mquerostudio/MQ-One/3-KiCad_library/3-3D/STPS140A.stp

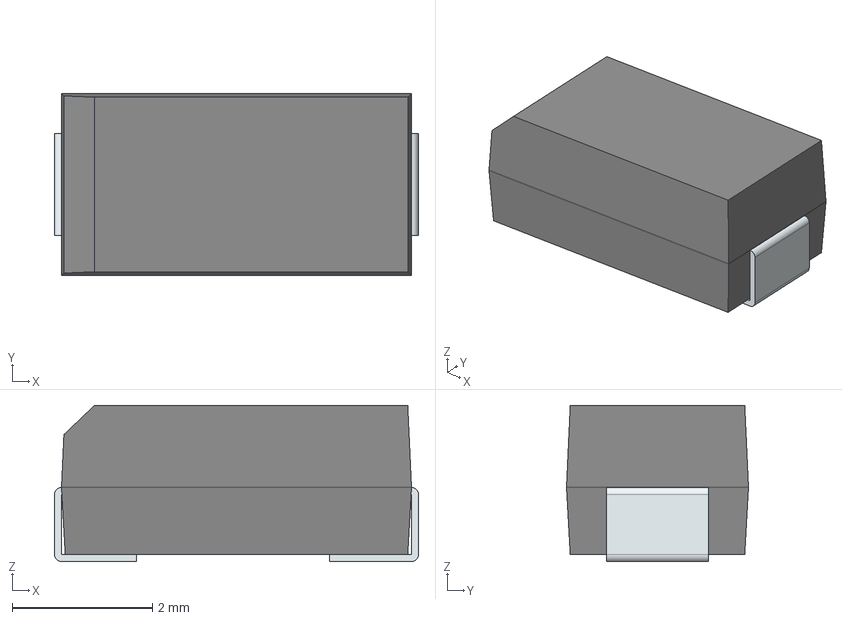
[picture p15: CAD file, 2024-10-10]
3-KiCad_library/3-3D/STPS140A.stp
5.20 x 2.60 x 2.23 mm
FilletPin1
FilletPin2
