mquerostudio/MQ-One/3-KiCad_library/3-3D/SIA527DJ-T1-GE3.stp

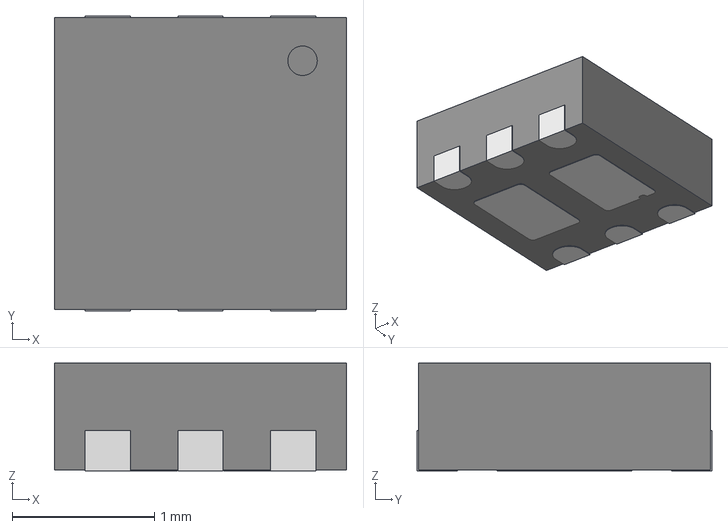
[picture p16: CAD file, 2024-10-10]
3-KiCad_library/3-3D/SIA527DJ-T1-GE3.stp
2.05 x 2.07 x 0.757 mm
