mquerostudio/MQ-One/3-KiCad_library/3-3D/USBLC6-2SC6.stp

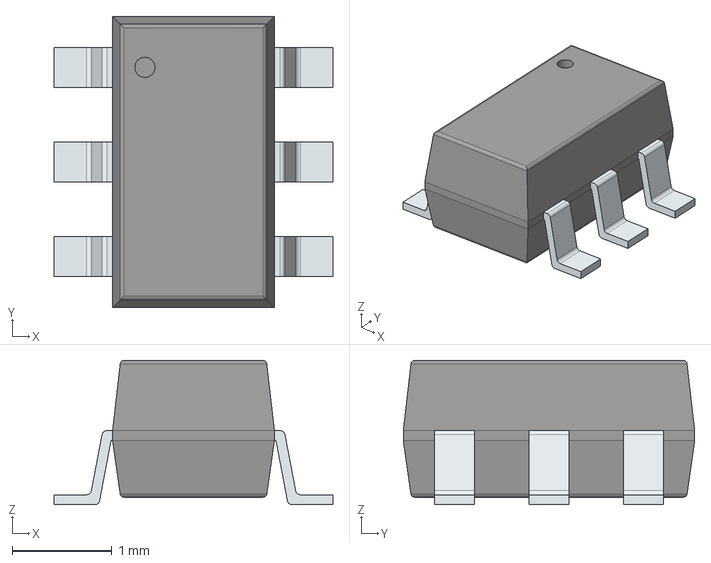
[picture p17: CAD file, 2024-10-10]
3-KiCad_library/3-3D/USBLC6-2SC6.stp
2.80 x 2.92 x 1.45 mm
PinsArrayLR
