mquerostudio/MQ-One/3-KiCad_library/3-3D/2-2328724-1.stp

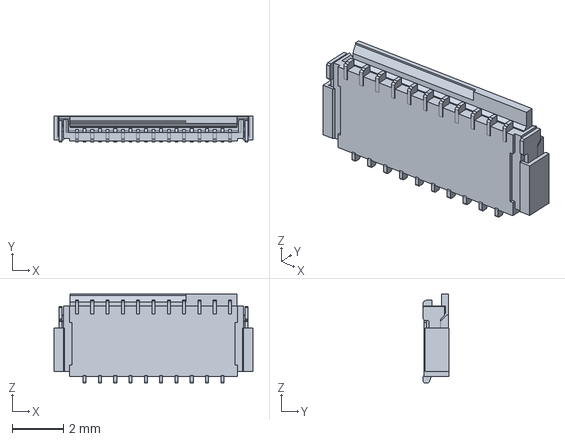
[picture p18: CAD file, 2024-10-10]
3-KiCad_library/3-3D/2-2328724-1.stp
7.80 x 1.00 x 3.48 mm
