mquerostudio/MQ-One/3-KiCad_library/3-3D/S2B-ZR-SM4A-TF.step

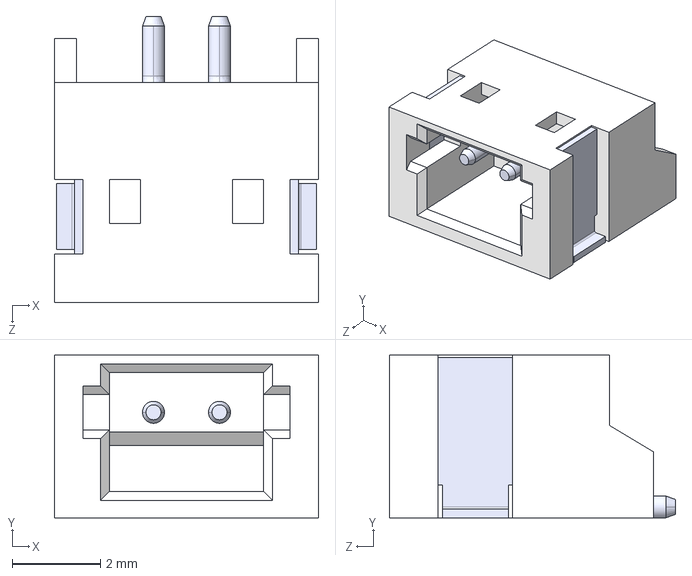
[picture p19: CAD file, 2024-10-10]
3-KiCad_library/3-3D/S2B-ZR-SM4A-TF.step
6.00 x 3.70 x 6.50 mm
