mquerostudio/MQ-One/3-KiCad_library/3-3D/ICS-43434.stp

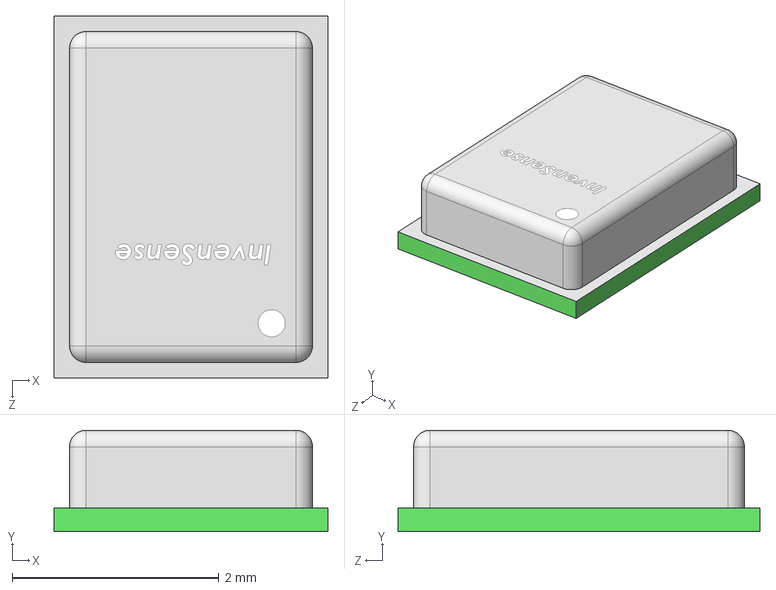
[picture p20: CAD file, 2024-10-10]
3-KiCad_library/3-3D/ICS-43434.stp
2.65 x 0.981 x 3.50 mm
