mquerostudio/MQ-One/3-KiCad_library/3-3D/MSD-1-A.stp

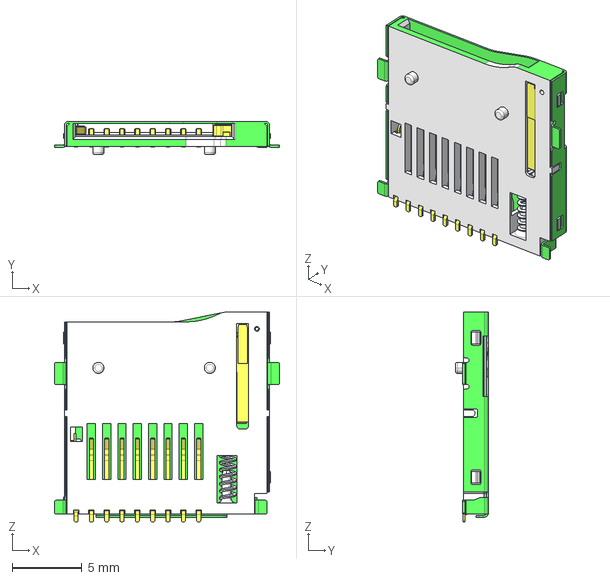
[picture p21: CAD file, 2024-10-10]
3-KiCad_library/3-3D/MSD-1-A.stp
16.1 x 2.40 x 15.0 mm
