mquerostudio/MQ-One/3-KiCad_library/3-3D/ASE-24.000MHZ-L-R-T.stp

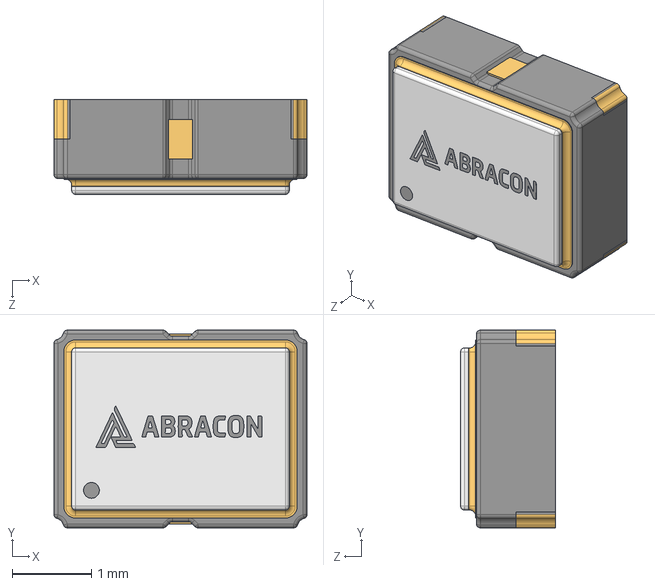
[picture p22: CAD file, 2024-10-10]
3-KiCad_library/3-3D/ASE-24.000MHZ-L-R-T.stp
3.20 x 2.50 x 1.20 mm
ASE-25.000MHZ-LR-T
Abracon New Logo
