mquerostudio/MQ-One/3-KiCad_library/3-3D/DSK-3R3H224U-HL.step

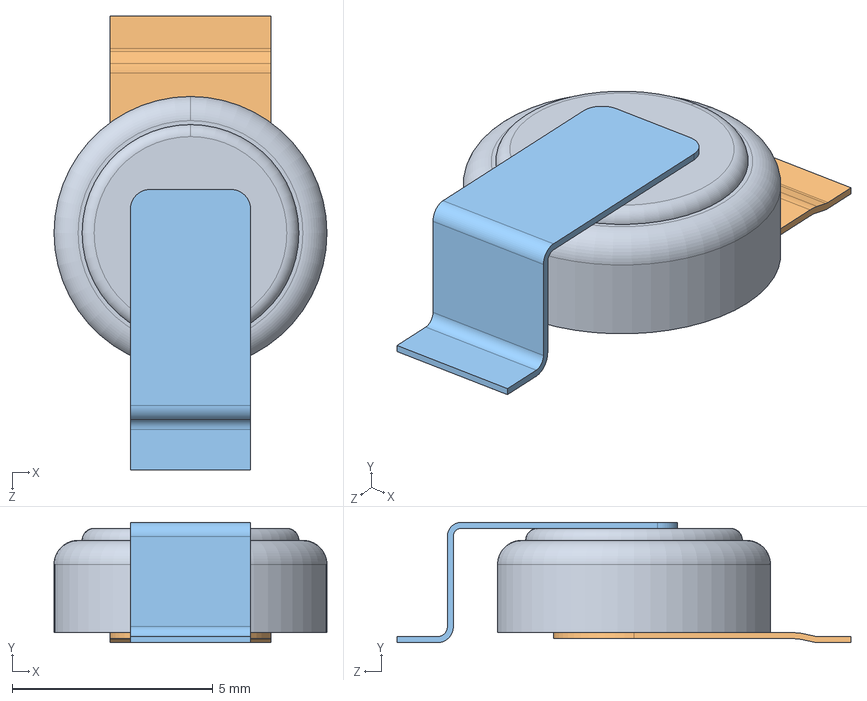
[picture p23: CAD file, 2024-10-10]
3-KiCad_library/3-3D/DSK-3R3H224U-HL.step
6.80 x 3.00 x 11.3 mm
