mquerostudio/MQ-One/3-KiCad_library/3-3D/FH35C-21S-0.3SHW.stp

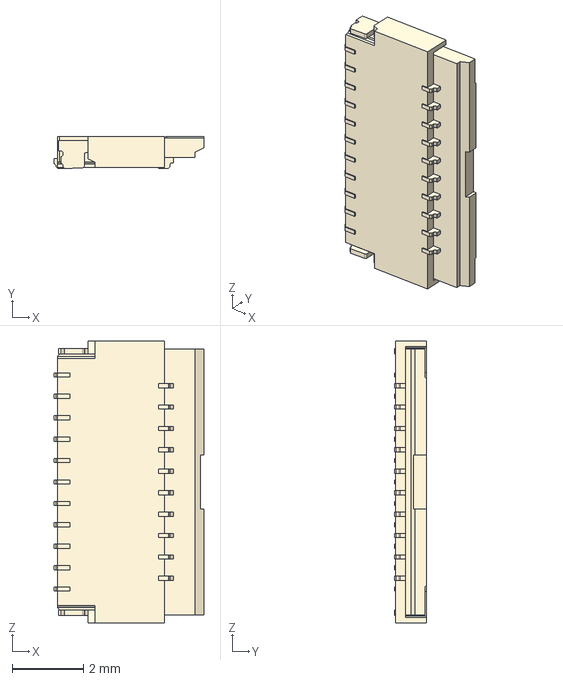
[picture p24: CAD file, 2024-10-10]
3-KiCad_library/3-3D/FH35C-21S-0.3SHW.stp
4.20 x 0.9 x 7.90 mm
