mquerostudio/MQ-One/3-KiCad_library/3-3D/PA1010D.step

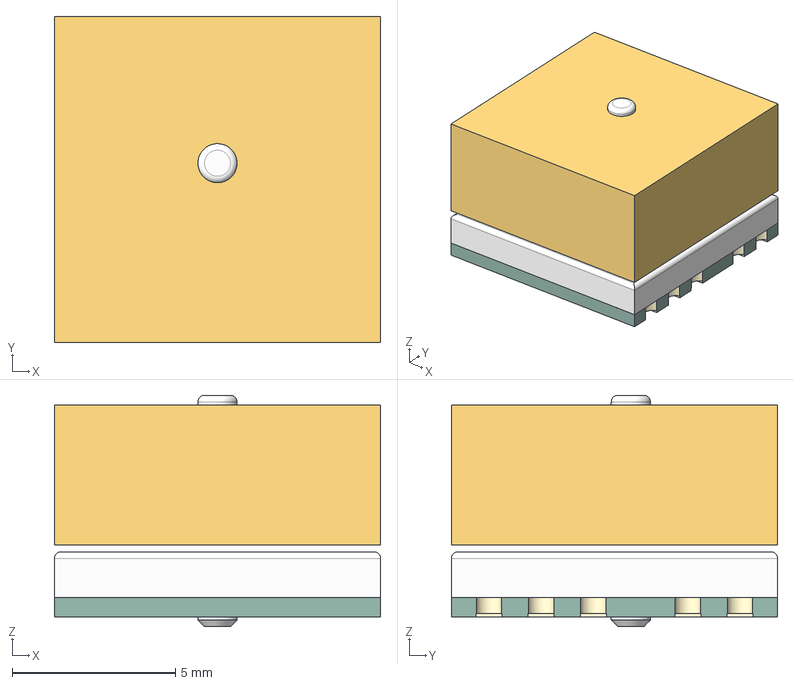
[picture p25: CAD file, 2024-10-10]
3-KiCad_library/3-3D/PA1010D.step
10.0 x 10.0 x 7.10 mm
