mquerostudio/MQ-One/3-KiCad_library/3-3D/PEC11R-4215F-S0024.step

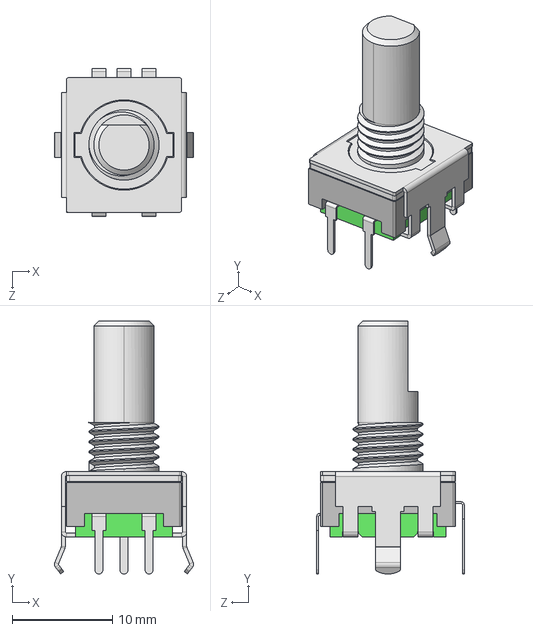
[picture p26: CAD file, 2024-10-10]
3-KiCad_library/3-3D/PEC11R-4215F-S0024.step
13.9 x 25.2 x 14.7 mm
