mquerostudio/MQ-One/3-KiCad_library/3-3D/BNO085.stp

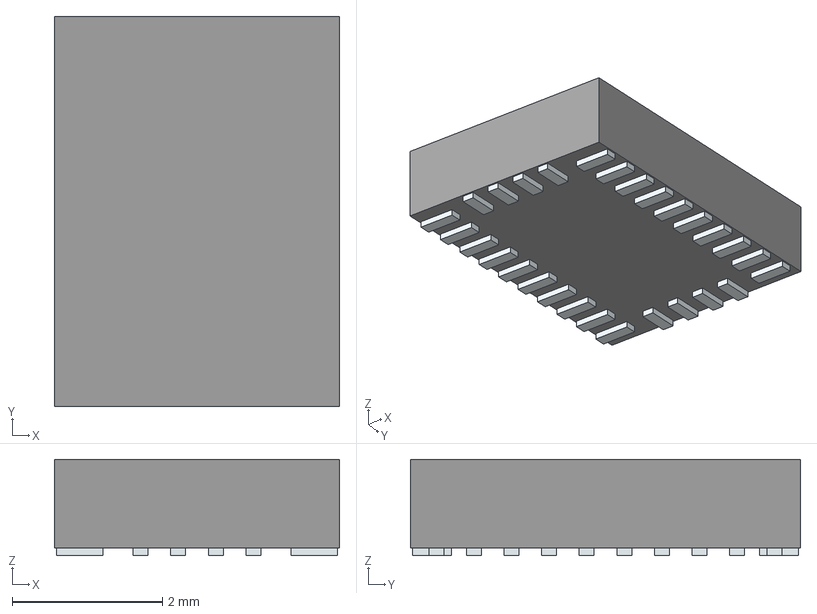
[picture p27: CAD file, 2024-10-10]
3-KiCad_library/3-3D/BNO085.stp
3.80 x 5.20 x 1.28 mm
Pins
