mquerostudio/MQ-One/3-KiCad_library/3-3D/ATSAMD21G18A-MUT.stp

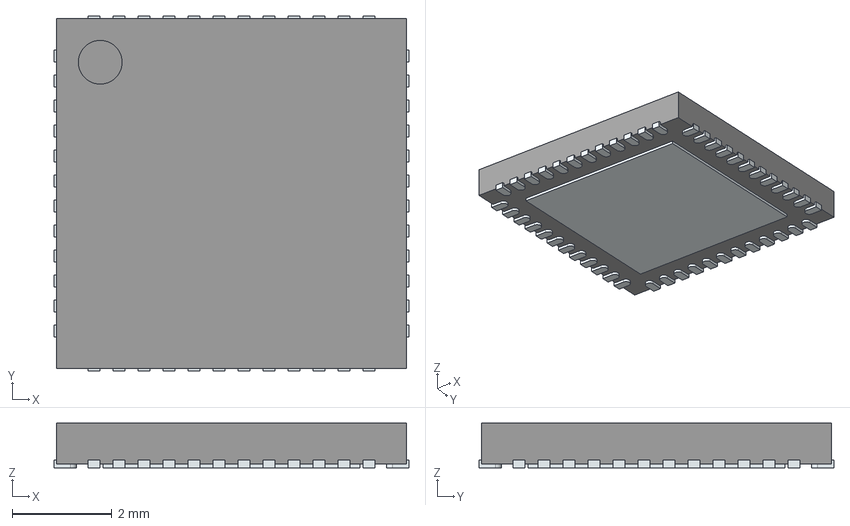
[picture p28: CAD file, 2024-10-10]
3-KiCad_library/3-3D/ATSAMD21G18A-MUT.stp
7.10 x 7.10 x 0.9 mm
ThermalPin
PinsArrayLR
PinsArrayTB
