mquerostudio/MQ-One/3-KiCad_library/3-3D/DESD3V3S1BL-7B.step

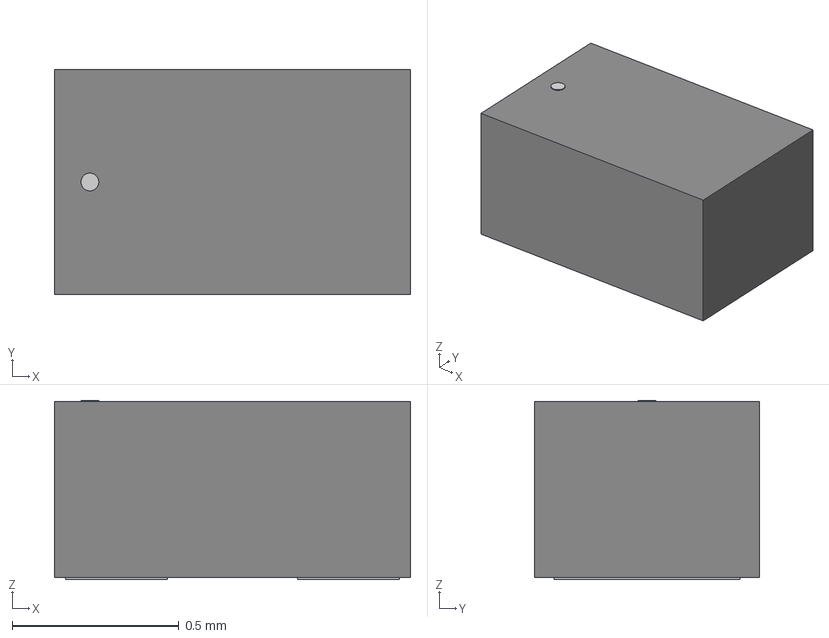
[picture p29: CAD file, 2024-10-10]
3-KiCad_library/3-3D/DESD3V3S1BL-7B.step
1.07 x 0.674 x 0.536 mm
