mquerostudio/MQ-One/3-KiCad_library/3-3D/NCV6324BMTAATBG.step

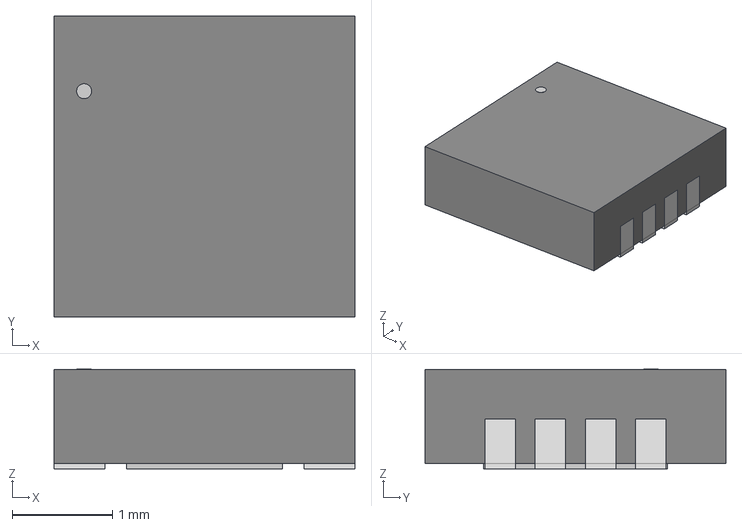
[picture p30: CAD file, 2024-10-10]
3-KiCad_library/3-3D/NCV6324BMTAATBG.step
3.00 x 3.00 x 0.993 mm
