mquerostudio/MQ-One/3-KiCad_library/3-3D/DS28E07P+.step

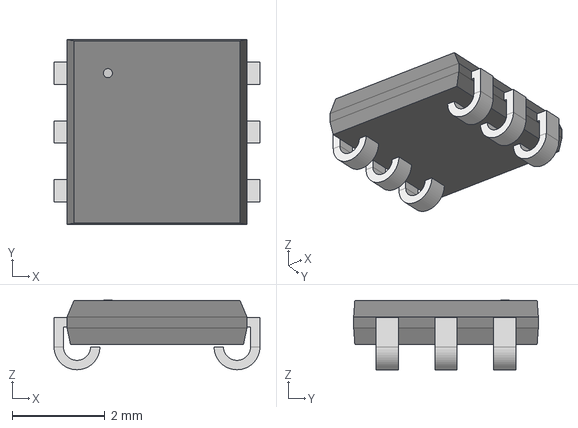
[picture p31: CAD file, 2024-10-10]
3-KiCad_library/3-3D/DS28E07P+.step
4.45 x 3.99 x 1.50 mm
