mquerostudio/MQ-One/3-KiCad_library/3-3D/BSS138-7-F.step

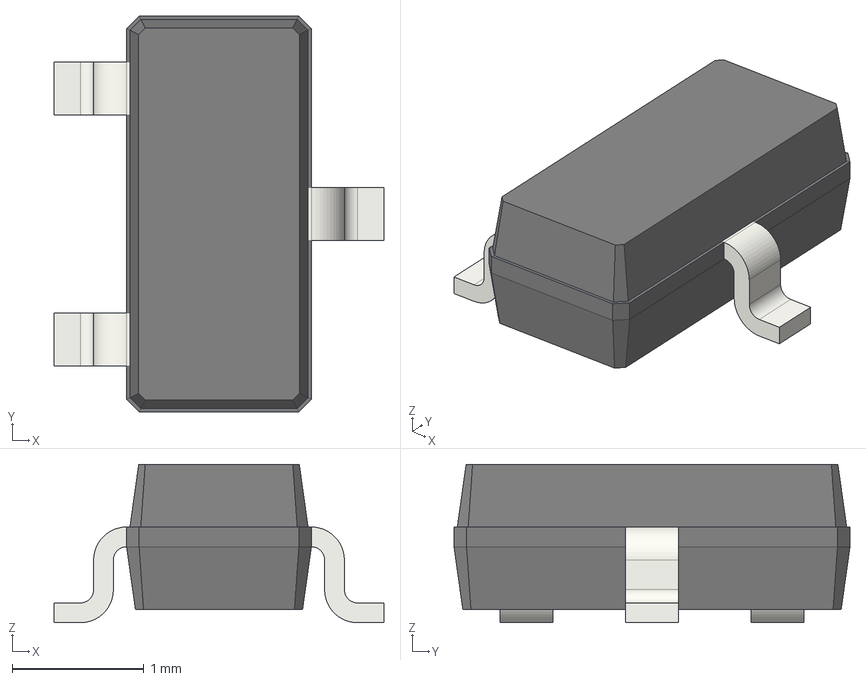
[picture p32: CAD file, 2024-10-10]
3-KiCad_library/3-3D/BSS138-7-F.step
2.50 x 3.00 x 1.20 mm
