mquerostudio/MQ-One/3-KiCad_library/3-3D/FD5640.step

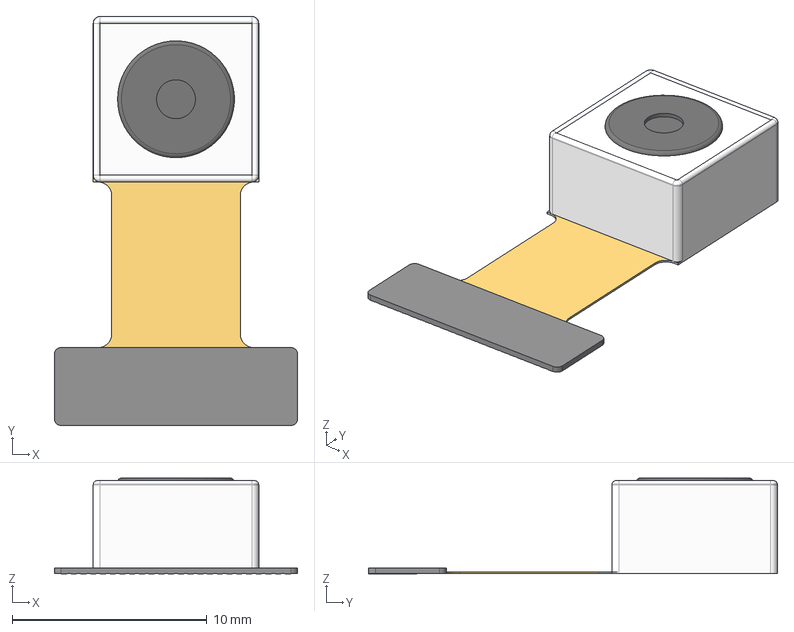
[picture p33: CAD file, 2024-10-10]
3-KiCad_library/3-3D/FD5640.step
12.5 x 21.0 x 4.92 mm
