mquerostudio/MQ-One/3-KiCad_library/3-3D/SP0503BAHTG.stp

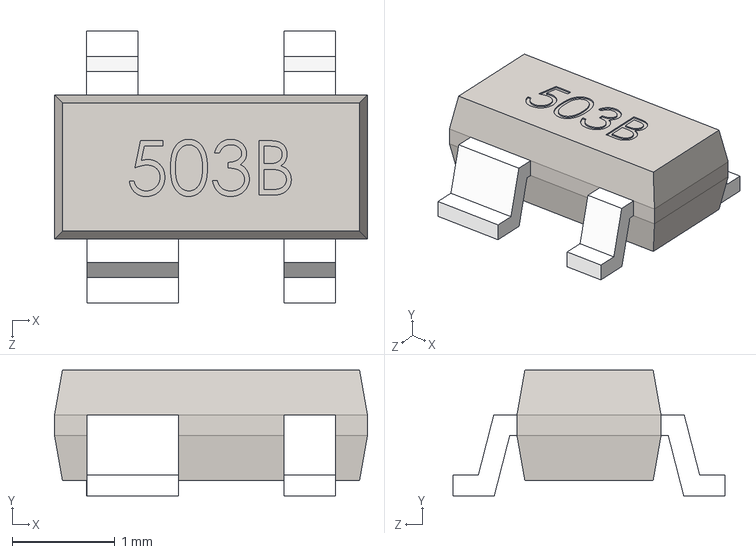
[picture p34: CAD file, 2024-10-10]
3-KiCad_library/3-3D/SP0503BAHTG.stp
3.04 x 1.22 x 2.64 mm
