mquerostudio/MQ-One/3-KiCad_library/3-3D/TFC-115-02-F-D-A.stp

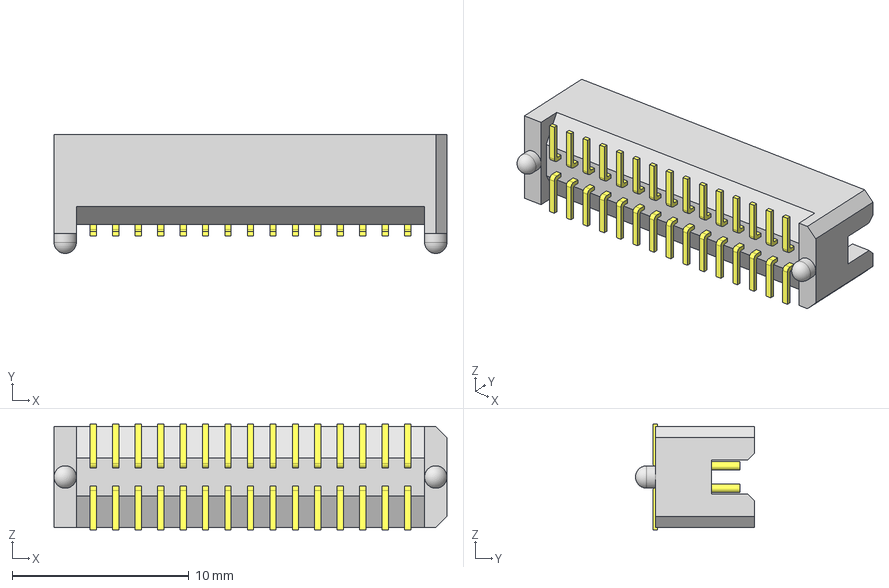
[picture p35: CAD file, 2024-10-10]
3-KiCad_library/3-3D/TFC-115-02-F-D-A.stp
22.2 x 6.73 x 5.97 mm
TFC-115-02-L-D-A_terminal
TFC-115-02-L-D_pins
