mquerostudio/MQ-One/3-KiCad_library/3-3D/9HT10-32.768KBZF-T.step

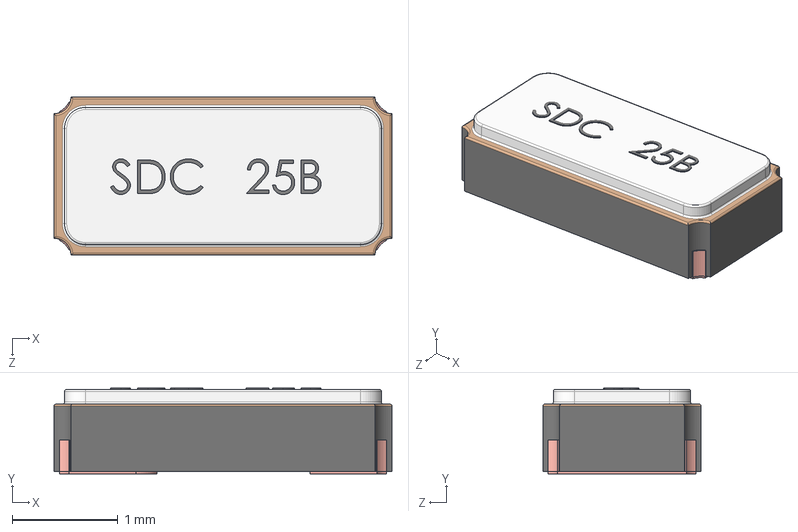
[picture p36: CAD file, 2024-10-10]
3-KiCad_library/3-3D/9HT10-32.768KBZF-T.step
3.20 x 0.81 x 1.50 mm
