mquerostudio/MQ-One/3-KiCad_library/3-3D/APDS-9960.stp

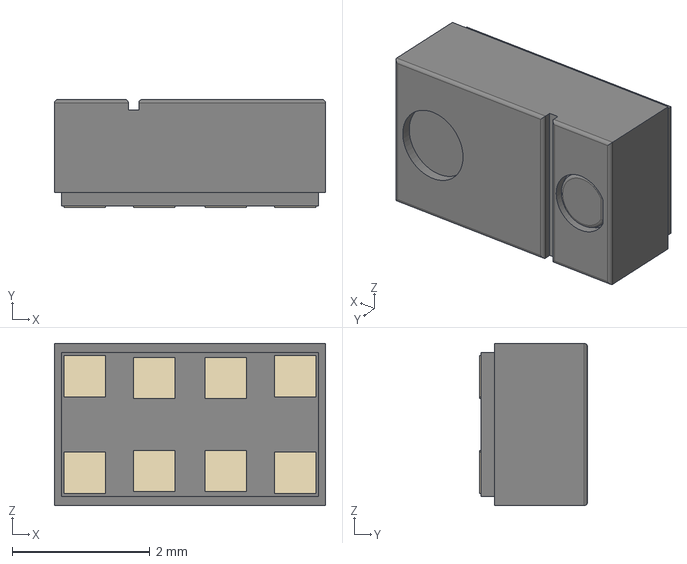
[picture p37: CAD file, 2024-10-10]
3-KiCad_library/3-3D/APDS-9960.stp
3.94 x 1.57 x 2.36 mm
