mquerostudio/MQ-One/3-KiCad_library/3-3D/LQH44PN1R0MPRL.STEP

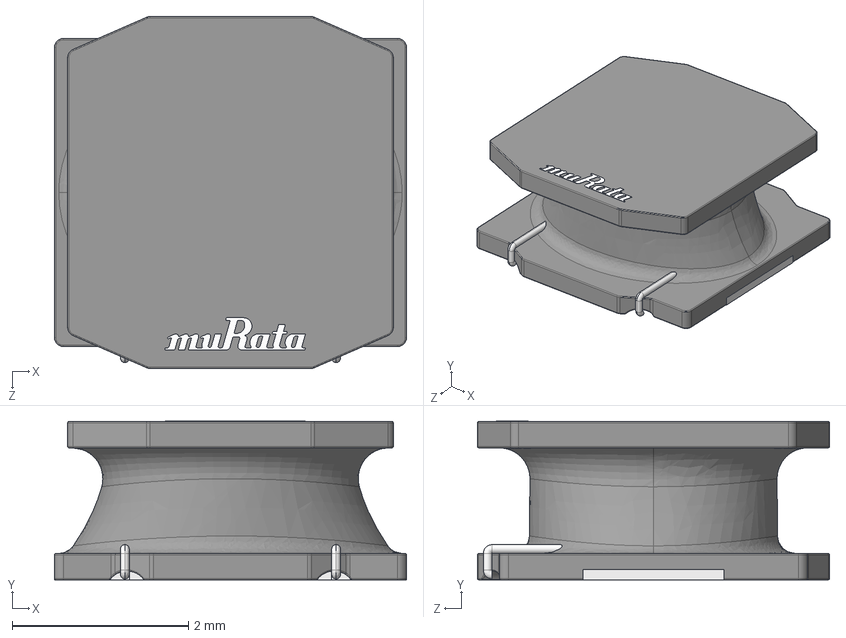
[picture p38: CAD file, 2024-10-10]
3-KiCad_library/3-3D/LQH44PN1R0MPRL.STEP
4.00 x 1.80 x 4.00 mm
logo
terminals
terminal wire
