mquerostudio/MQ-One/3-KiCad_library/3-3D/SFC-115-T2-F-D-A-K.step

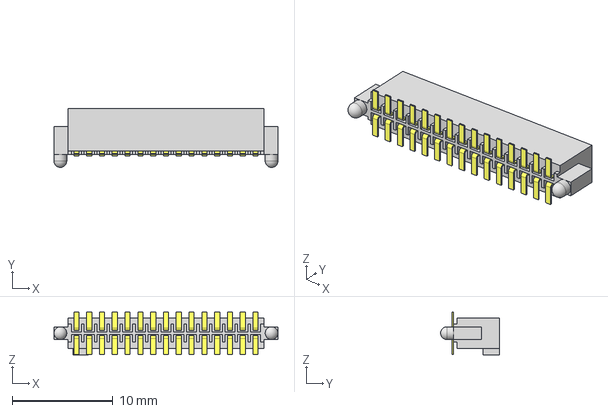
[picture p39: CAD file, 2024-10-10]
3-KiCad_library/3-3D/SFC-115-T2-F-D-A-K.step
22.2 x 5.84 x 4.25 mm
SFC-115-T2-D-A_terminal
C-119-T2-15_pins
