mquerostudio/MQ-One/3-KiCad_library/3-3D/BAT54CWT1G.stp

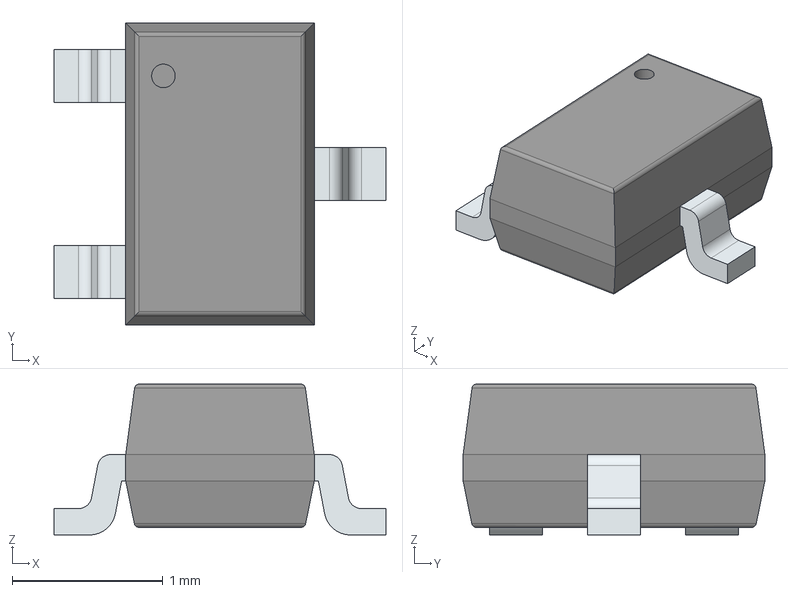
[picture p40: CAD file, 2024-10-10]
3-KiCad_library/3-3D/BAT54CWT1G.stp
2.20 x 2.00 x 1.00 mm
PinsArrayL
FilletPinR
