mquerostudio/MQ-One/3-KiCad_library/3-3D/ATSAMD09D14A-MUT.stp

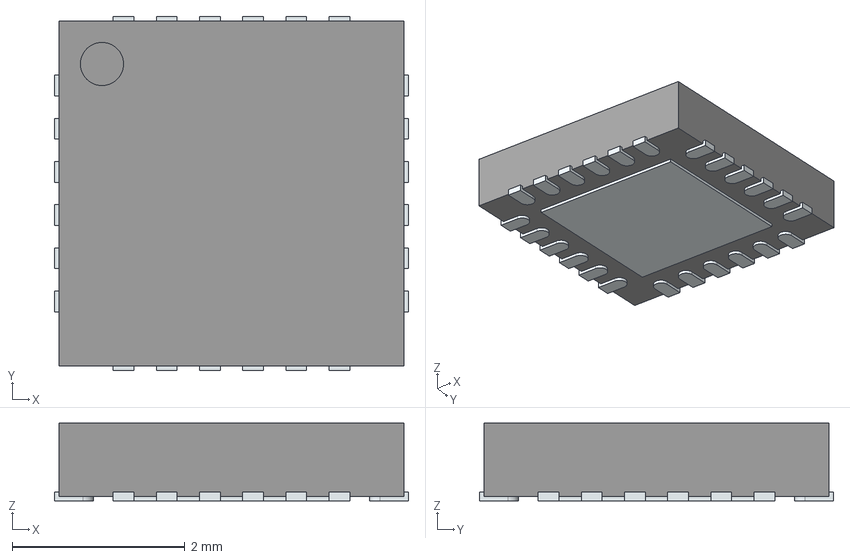
[picture p41: CAD file, 2024-10-10]
3-KiCad_library/3-3D/ATSAMD09D14A-MUT.stp
4.10 x 4.10 x 0.9 mm
ThermalPin
PinsArrayLR
PinsArrayTB
