mquerostudio/MQ-One/1-Proof of Concept (POC)/3-Firmware/bme280test/bme280test.ino

/*
  Rui Santos
  Complete project details at https://RandomNerdTutorials.com/esp32-i2c-communication-arduino-ide/
  
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
  The above copyright notice and this permission notice shall be included in all
  copies or substantial portions of the Software.
*/

#include <Wire.h>
#include <Adafruit_Sensor.h>
#include <Adafruit_BME280.h>

#define I2C_SDA 8
#define I2C_SCL 18

#define SEALEVELPRESSURE_HPA (1013.25)

TwoWire I2CBME = TwoWire(0);
Adafruit_BME280 bme;

unsigned long delayTime;

void setup() {
  Serial.begin(115200);
  Serial.println(F("BME280 test"));
  I2CBME.begin(I2C_SDA, I2C_SCL, 100000);

  bool status;

  // default settings
  // (you can also pass in a Wire library object like &Wire2)
  status = bme.begin(0x77, &I2CBME);  
  if (!status) {
    Serial.println("Could not find a valid BME280 sensor, check wiring!");
    while (1);
  }

  Serial.println("-- Default Test --");
  delayTime = 1000;

  Serial.println();
}

void loop() { 
  printValues();
  delay(delayTime);
}

void printValues() {
  Serial.print("Temperature = ");
  Serial.print(bme.readTemperature());
  Serial.println(" *C");
  
  // Convert temperature to Fahrenheit
  /*Serial.print("Temperature = ");
  Serial.print(1.8 * bme.readTemperature() + 32);
  Serial.println(" *F");*/
  
  Serial.print("Pressure = ");
  Serial.print(bme.readPressure() / 100.0F);
  Serial.println(" hPa");

  Serial.print("Approx. Altitude = ");
  Serial.print(bme.readAltitude(SEALEVELPRESSURE_HPA));
  Serial.println(" m");

  Serial.print("Humidity = ");
  Serial.print(bme.readHumidity());
  Serial.println(" %");

  Serial.println();
}
