mquerostudio/MQ-One/2-Engineering Validation Test (EVT)/3-Firmware/1-TestFW/BME280/BME280.ino

#include <Wire.h>
#include <Adafruit_Sensor.h>
#include <Adafruit_BME280.h>

#define SEALEVELPRESSURE_HPA (1013.25)

Adafruit_BME280 bme; // I2C

unsigned long delayTime;

void setup() {
    Serial.begin(9600);
    while(!Serial);    // Wait until serial is ready

    Serial.println(F("BME280 test"));

    // Initialize I2C communication on custom SDA and SCL pins
    Wire.begin(9, 10);  // SDA on pin 9, SCL on pin 10

    unsigned status;
    
    // Default settings; start communication using I2C
    status = bme.begin(0x77, &Wire);  // Here you may need to adjust the address
                                      // if your device uses the alternative 0x77
    if (!status) {
        Serial.println("Could not find a valid BME280 sensor, check wiring, address, sensor ID!");
        Serial.print("SensorID was: 0x"); Serial.println(bme.sensorID(), 16);
        Serial.print("        ID of 0xFF probably means a bad address, a BMP 180 or BMP 085\n");
        Serial.print("   ID of 0x56-0x58 represents a BMP 280,\n");
        Serial.print("        ID of 0x60 represents a BME 280.\n");
        Serial.print("        ID of 0x61 represents a BME 680.\n");
        while (1) delay(10);
    }
    
    Serial.println("-- Default Test --");
    delayTime = 1000;

    Serial.println();
}


void loop() { 
    printValues();
    delay(delayTime);
}


void printValues() {
    Serial.print("Temperature = ");
    Serial.print(bme.readTemperature());
    Serial.println(" °C");

    Serial.print("Pressure = ");
    Serial.print(bme.readPressure() / 100.0F);
    Serial.println(" hPa");

    Serial.print("Approx. Altitude = ");
    Serial.print(bme.readAltitude(SEALEVELPRESSURE_HPA));
    Serial.println(" m");

    Serial.print("Humidity = ");
    Serial.print(bme.readHumidity());
    Serial.println(" %");

    Serial.println();
}
