mquerostudio/MQ-One/2-Engineering Validation Test (EVT)/3-Firmware/2-MQOneOS/main/lv_port_indev.c

/**
 * @file lv_port_indev.c
 *
 */

/*Copy this file as "lv_port_indev.c" and set this value to "1" to enable
 * content*/
#include "esp_lcd_touch.h"
#include <stdint.h>
#if 1

/*********************
 *      INCLUDES
 *********************/
#include "lv_port_indev.h"

/*********************
 *      DEFINES
 *********************/

/**********************
 *      TYPEDEFS
 **********************/
esp_lcd_touch_handle_t tp_handle = NULL;

/**********************
 *  STATIC PROTOTYPES
 **********************/

static void touchpad_init(void);
static void touchpad_read(lv_indev_t *indev, lv_indev_data_t *data);
/*static bool touchpad_is_pressed(int32_t * x, int32_t * y);*/

// static void mouse_init(void);
// static void mouse_read(lv_indev_t * indev, lv_indev_data_t * data);
// static bool mouse_is_pressed(void);
// static void mouse_get_xy(int32_t * x, int32_t * y);

// static void keypad_init(void);
// static void keypad_read(lv_indev_t * indev, lv_indev_data_t * data);
// static uint32_t keypad_get_key(void);

static void encoder_init(void);
static void encoder_read(lv_indev_t *indev, lv_indev_data_t *data);
static void encoder_handler(void);

// static void button_init(void);
// static void button_read(lv_indev_t * indev, lv_indev_data_t * data);
// static int8_t button_get_pressed_id(void);
// static bool button_is_pressed(uint8_t id);

/**********************
 *  STATIC VARIABLES
 **********************/
lv_indev_t *indev_touchpad;
// lv_indev_t * indev_mouse;
// lv_indev_t * indev_keypad;
lv_indev_t *indev_encoder;
// lv_indev_t * indev_button;

static int32_t encoder_diff;
static lv_indev_state_t encoder_state;

/**********************
 *      MACROS
 **********************/

/**********************
 *   GLOBAL FUNCTIONS
 **********************/

void lv_port_indev_init(void) {
  /**
   * Here you will find example implementation of input devices supported by
   * LittelvGL:
   *  - Touchpad
   *  - Mouse (with cursor support)
   *  - Keypad (supports GUI usage only with key)
   *  - Encoder (supports GUI usage only with: left, right, push)
   *  - Button (external buttons to press points on the screen)
   *
   *  The `..._read()` function are only examples.
   *  You should shape them according to your hardware
   */

  /*------------------
   * Touchpad
   * -----------------*/

  /*Initialize your touchpad if you have*/
  touchpad_init();

  /*Register a touchpad input device*/
  indev_touchpad = lv_indev_create();
  lv_indev_set_type(indev_touchpad, LV_INDEV_TYPE_POINTER);
  lv_indev_set_read_cb(indev_touchpad, touchpad_read);

  /*------------------
   * Mouse
   * -----------------*/

  // /*Initialize your mouse if you have*/
  // mouse_init();

  // /*Register a mouse input device*/
  // indev_mouse = lv_indev_create();
  // lv_indev_set_type(indev_mouse, LV_INDEV_TYPE_POINTER);
  // lv_indev_set_read_cb(indev_mouse, mouse_read);

  // /*Set cursor. For simplicity set a HOME symbol now.*/
  // lv_obj_t * mouse_cursor = lv_image_create(lv_screen_active());
  // lv_image_set_src(mouse_cursor, LV_SYMBOL_HOME);
  // lv_indev_set_cursor(indev_mouse, mouse_cursor);

  /*------------------
   * Keypad
   * -----------------*/

  // /*Initialize your keypad or keyboard if you have*/
  // keypad_init();

  // /*Register a keypad input device*/
  // indev_keypad = lv_indev_create();
  // lv_indev_set_type(indev_keypad, LV_INDEV_TYPE_KEYPAD);
  // lv_indev_set_read_cb(indev_keypad, keypad_read);

  /*Later you should create group(s) with `lv_group_t * group =
   *lv_group_create()`, add objects to the group with `lv_group_add_obj(group,
   *obj)` and assign this input device to group to navigate in it:
   *`lv_indev_set_group(indev_keypad, group);`*/

  /*------------------
   * Encoder
   * -----------------*/

  /*Initialize your encoder if you have*/
  /*encoder_init();*/

  /*Register a encoder input device*/
  /*indev_encoder = lv_indev_create();
  lv_indev_set_type(indev_encoder, LV_INDEV_TYPE_ENCODER);
  lv_indev_set_read_cb(indev_encoder, encoder_read);*/

  /*Later you should create group(s) with `lv_group_t * group =
   *lv_group_create()`, add objects to the group with `lv_group_add_obj(group,
   *obj)` and assign this input device to group to navigate in it:
   *`lv_indev_set_group(indev_encoder, group);`*/

  /*------------------
   * Button
   * -----------------*/

  // /*Initialize your button if you have*/
  // button_init();

  // /*Register a button input device*/
  // indev_button = lv_indev_create();
  // lv_indev_set_type(indev_button, LV_INDEV_TYPE_BUTTON);
  // lv_indev_set_read_cb(indev_button, button_read);

  // /*Assign buttons to points on the screen*/
  // static const lv_point_t btn_points[2] = {
  //     {10, 10},   /*Button 0 -> x:10; y:10*/
  //     {40, 100},  /*Button 1 -> x:40; y:100*/
  // };
  // lv_indev_set_button_points(indev_button, btn_points);
}

/**********************
 *   STATIC FUNCTIONS
 **********************/

/*------------------
 * Touchpad
 * -----------------*/

/*Initialize your touchpad*/
static void touchpad_init(void) {
  esp_lcd_panel_io_handle_t tp_io_handle = NULL;
  esp_lcd_panel_io_i2c_config_t tp_io_config =
      ESP_LCD_TOUCH_IO_I2C_CST816S_CONFIG();
  tp_io_config.scl_speed_hz = (400 * 1000);
  ESP_ERROR_CHECK(esp_lcd_new_panel_io_i2c(board_i2c_bus_handle, &tp_io_config,
                                           &tp_io_handle));

  esp_lcd_touch_config_t tp_cfg = {
      .x_max = CONFIG_LCD_H_RES,
      .y_max = CONFIG_LCD_V_RES,
      .rst_gpio_num = BOARD_TOUCH_RST,
      .int_gpio_num = BOARD_TOUCH_IRQ,
      .levels =
          {
              .reset = 0,
              .interrupt = 0,
          },
      .flags =
          {
              .swap_xy = 0,
              .mirror_x = 0,
              .mirror_y = 0,
          },
      .interrupt_callback = NULL,
      .process_coordinates = NULL,
  };
  esp_lcd_touch_new_i2c_cst816s(tp_io_handle, &tp_cfg, &tp_handle);
}

/*Will be called by the library to read the touchpad*/
static void touchpad_read(lv_indev_t *indev_drv, lv_indev_data_t *data) {
  uint16_t touch_x[1];
  uint16_t touch_y[1];
  uint8_t touch_cnt = 0;

  esp_lcd_touch_read_data(tp_handle);
  bool touchpad_is_pressed = esp_lcd_touch_get_coordinates(
      tp_handle, touch_x, touch_y, NULL, &touch_cnt, 1);

  /*Save the pressed coordinates and the state*/
  if (touchpad_is_pressed) {
    data->state = LV_INDEV_STATE_PRESSED;
    data->point.x = touch_x[0];
    data->point.y = touch_y[0];

    // Log the touch coordinates
    // ESP_LOGI("Touchpad", "Pressed at x: %d, y: %d", touch_x[0], touch_y[0]);
  } else {
    data->state = LV_INDEV_STATE_RELEASED;
  }
}

/*Return true is the touchpad is pressed*/
/*static bool touchpad_is_pressed(int32_t * x, int32_t * y)
{
    static uint8_t touch_cnt = 0;

    return esp_lcd_touch_get_coordinates(tp_handle, (uint16_t*) x, (uint16_t*)
y, NULL, &touch_cnt, 1);
}*/

/*------------------
 * Mouse
 * -----------------*/

// /*Initialize your mouse*/
// static void mouse_init(void)
// {
//     /*Your code comes here*/
// }

// /*Will be called by the library to read the mouse*/
// static void mouse_read(lv_indev_t * indev_drv, lv_indev_data_t * data)
// {
//     /*Get the current x and y coordinates*/
//     mouse_get_xy(&data->point.x, &data->point.y);

//     /*Get whether the mouse button is pressed or released*/
//     if(mouse_is_pressed()) {
//         data->state = LV_INDEV_STATE_PRESSED;
//     }
//     else {
//         data->state = LV_INDEV_STATE_RELEASED;
//     }
// }

// /*Return true is the mouse button is pressed*/
// static bool mouse_is_pressed(void)
// {
//     /*Your code comes here*/

//     return false;
// }

// /*Get the x and y coordinates if the mouse is pressed*/
// static void mouse_get_xy(int32_t * x, int32_t * y)
// {
//     /*Your code comes here*/

//     (*x) = 0;
//     (*y) = 0;
// }

/*------------------
 * Keypad
 * -----------------*/

// /*Initialize your keypad*/
// static void keypad_init(void)
// {
//     /*Your code comes here*/
// }

// /*Will be called by the library to read the mouse*/
// static void keypad_read(lv_indev_t * indev_drv, lv_indev_data_t * data)
// {
//     static uint32_t last_key = 0;

//     /*Get the current x and y coordinates*/
//     mouse_get_xy(&data->point.x, &data->point.y);

//     /*Get whether the a key is pressed and save the pressed key*/
//     uint32_t act_key = keypad_get_key();
//     if(act_key != 0) {
//         data->state = LV_INDEV_STATE_PRESSED;

//         /*Translate the keys to LVGL control characters according to your key
//         definitions*/ switch(act_key) {
//             case 1:
//                 act_key = LV_KEY_NEXT;
//                 break;
//             case 2:
//                 act_key = LV_KEY_PREV;
//                 break;
//             case 3:
//                 act_key = LV_KEY_LEFT;
//                 break;
//             case 4:
//                 act_key = LV_KEY_RIGHT;
//                 break;
//             case 5:
//                 act_key = LV_KEY_ENTER;
//                 break;
//         }

//         last_key = act_key;
//     }
//     else {
//         data->state = LV_INDEV_STATE_RELEASED;
//     }

//     data->key = last_key;
// }

// /*Get the currently being pressed key.  0 if no key is pressed*/
// static uint32_t keypad_get_key(void)
// {
//     /*Your code comes here*/

//     return 0;
// }

/*------------------
 * Encoder
 * -----------------*/

/*Initialize your encoder*/
static void encoder_init(void) { /*Your code comes here*/ }

/*Will be called by the library to read the encoder*/
static void encoder_read(lv_indev_t *indev_drv, lv_indev_data_t *data) {
  /*Get the encoder diff and button state*/
  encoder_handler();
  data->enc_diff = encoder_diff;
  data->state = encoder_state;

  // ESP_LOGI("Encoder", "Diff: %d, State: %d", (int16_t)encoder_diff,
  // (uint16_t)encoder_state);
}

/*Call this function in an interrupt to process encoder events (turn, press)*/
static void encoder_handler(void) {
  encoder_diff = seesaw_encoder_get_delta(seesaw_handle);
  if (gpio_get_level(PIN_ENCODER_SW) == 0)
    encoder_state = LV_INDEV_STATE_PRESSED;
  else
    encoder_state = LV_INDEV_STATE_RELEASED;
}

// /*------------------
//  * Button
//  * -----------------*/

// /*Initialize your buttons*/
// static void button_init(void)
// {
//     /*Your code comes here*/
// }

// /*Will be called by the library to read the button*/
// static void button_read(lv_indev_t * indev_drv, lv_indev_data_t * data)
// {

//     static uint8_t last_btn = 0;

//     /*Get the pressed button's ID*/
//     int8_t btn_act = button_get_pressed_id();

//     if(btn_act >= 0) {
//         data->state = LV_INDEV_STATE_PRESSED;
//         last_btn = btn_act;
//     }
//     else {
//         data->state = LV_INDEV_STATE_RELEASED;
//     }

//     /*Save the last pressed button's ID*/
//     data->btn_id = last_btn;
// }

// /*Get ID  (0, 1, 2 ..) of the pressed button*/
// static int8_t button_get_pressed_id(void)
// {
//     uint8_t i;

//     /*Check to buttons see which is being pressed (assume there are 2
//     buttons)*/ for(i = 0; i < 2; i++) {
//         /*Return the pressed button's ID*/
//         if(button_is_pressed(i)) {
//             return i;
//         }
//     }

//     /*No button pressed*/
//     return -1;
// }

// /*Test if `id` button is pressed or not*/
// static bool button_is_pressed(uint8_t id)
// {

//     /*Your code comes here*/

//     return false;
// }

#else /*Enable this file at the top*/

/*This dummy typedef exists purely to silence -Wpedantic.*/
typedef int keep_pedantic_happy;
#endif
