mquerostudio/MQ-One/2-Engineering Validation Test (EVT)/3-Firmware/1-TestFW/MQ1_stepper/interface.h

// array size is 6589
static const byte base[] PROGMEM  = {
  0x89, 0x50, 0x4e, 0x47, 0x0d, 0x0a, 0x1a, 0x0a, 0x00, 0x00, 0x00, 0x0d, 0x49, 0x48, 0x44, 0x52, 
  0x00, 0x00, 0x00, 0xf0, 0x00, 0x00, 0x01, 0x40, 0x08, 0x06, 0x00, 0x00, 0x00, 0x82, 0xe8, 0xf1, 
  0x53, 0x00, 0x00, 0x01, 0x84, 0x69, 0x43, 0x43, 0x50, 0x49, 0x43, 0x43, 0x20, 0x70, 0x72, 0x6f, 
  0x66, 0x69, 0x6c, 0x65, 0x00, 0x00, 0x28, 0x91, 0x7d, 0x91, 0x3d, 0x48, 0xc3, 0x50, 0x14, 0x85, 
  0x4f, 0x53, 0xa5, 0x22, 0x15, 0x07, 0x3b, 0x88, 0x88, 0x64, 0xa8, 0x9d, 0x2c, 0x88, 0x15, 0x71, 
  0x94, 0x2a, 0x16, 0xc1, 0x42, 0x69, 0x2b, 0xb4, 0xea, 0x60, 0xf2, 0xd2, 0x3f, 0x68, 0xd2, 0x90, 
  0xa4, 0xb8, 0x38, 0x0a, 0xae, 0x05, 0x07, 0x7f, 0x16, 0xab, 0x0e, 0x2e, 0xce, 0xba, 0x3a, 0xb8, 
  0x0a, 0x82, 0xe0, 0x0f, 0x88, 0xb3, 0x83, 0x93, 0xa2, 0x8b, 0x94, 0x78, 0x5f, 0x52, 0x68, 0x11, 
  0xe3, 0x83, 0xcb, 0xfb, 0x38, 0xef, 0x9d, 0xc3, 0x7d, 0xf7, 0x01, 0x42, 0xb3, 0xca, 0x54, 0xb3, 
  0x67, 0x12, 0x50, 0x35, 0xcb, 0x48, 0x27, 0xe2, 0x62, 0x2e, 0xbf, 0x2a, 0x06, 0x5e, 0x11, 0xc0, 
  0x18, 0x55, 0x0c, 0x11, 0x89, 0x99, 0x7a, 0x32, 0xb3, 0x98, 0x85, 0xe7, 0xfa, 0xba, 0x87, 0x8f, 
  0xef, 0x77, 0x51, 0x9e, 0xe5, 0x7d, 0xef, 0xcf, 0x35, 0xa0, 0x14, 0x4c, 0x06, 0xf8, 0x44, 0xe2, 
  0x39, 0xa6, 0x1b, 0x16, 0xf1, 0x06, 0xf1, 0xcc, 0xa6, 0xa5, 0x73, 0xde, 0x27, 0x0e, 0xb1, 0xb2, 
  0xa4, 0x10, 0x9f, 0x13, 0x4f, 0x18, 0xd4, 0x20, 0xf1, 0x23, 0xd7, 0x65, 0x97, 0xdf, 0x38, 0x97, 
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
  0x92, 0xac, 0x1f, 0xe6, 0xc7, 0xa9, 0x73, 0xff, 0xe8, 0x9e, 0xef, 0xed, 0xe8, 0xf7, 0x39, 0xa7, 
  0x1f, 0xa7, 0x5e, 0xcf, 0xc7, 0xc3, 0x43, 0x9d, 0xbe, 0xdf, 0x4f, 0xe7, 0x7c, 0xbe, 0xe7, 0xdd, 
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
};
